foldedtoad/caliper_keyboard/images/debug_adapter_1.jpg

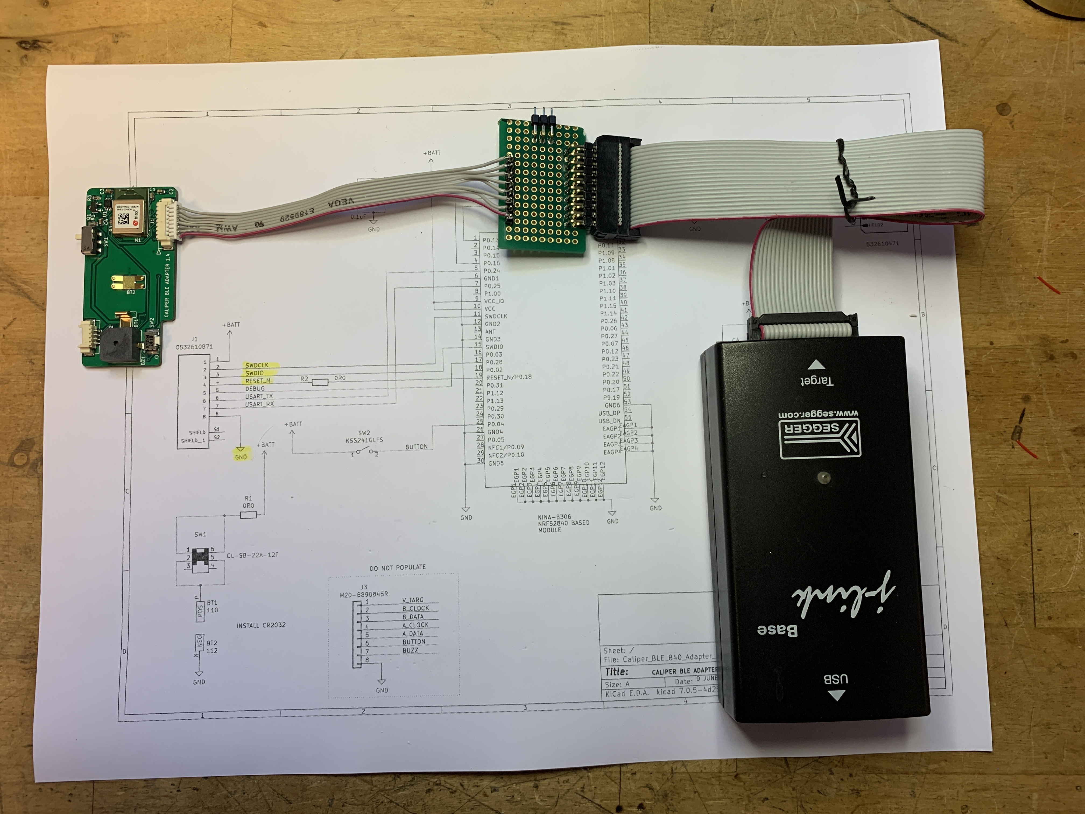
images/debug_adapter_1.jpg
