foldedtoad/caliper_keyboard/images/debug_adapter_2.jpg

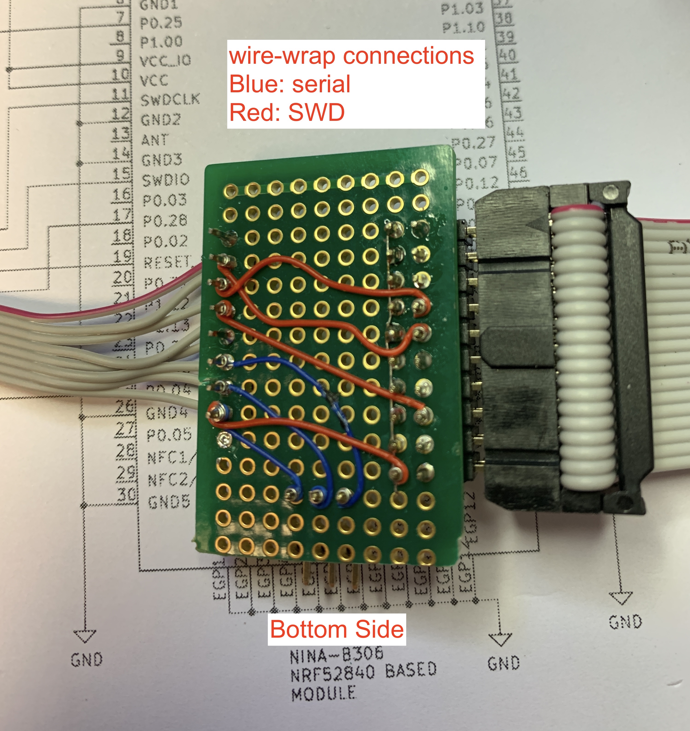
images/debug_adapter_2.jpg
