foldedtoad/caliper_keyboard/images/debug_adapter_3.JPG

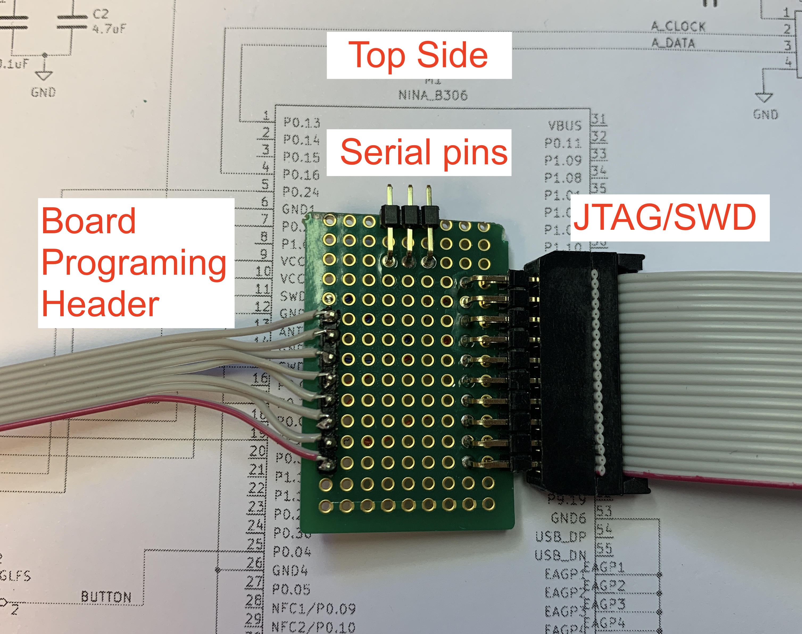
images/debug_adapter_3.JPG
