foldedtoad/caliper_keyboard/images/debug_cable.jpg

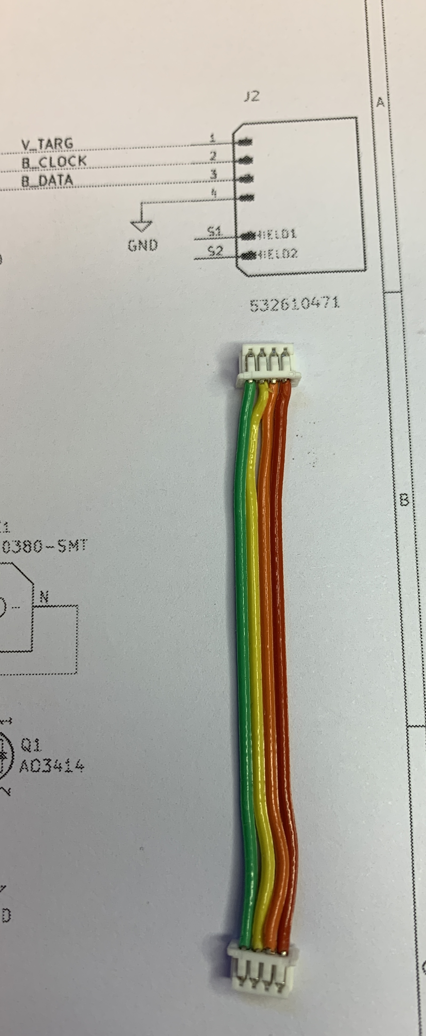
images/debug_cable.jpg
