foldedtoad/caliper_keyboard/inc/main.h

/*
 *  main.h 
 *
 *  Copyright (c) 2023   Callender-Consulting
 *
 *  SPDX-License-Identifier: Apache-2.0
 */
#ifndef __MAIN_H__
#define __MAIN_H__

/*---------------------------------------------------------------------------*/
/*                                                                           */
/*---------------------------------------------------------------------------*/

bool is_alt_running(void);

#endif /* __MAIN_H__ */
