foldedtoad/caliper_keyboard/inc/buzzer.h

/*
 *  buzzer.h  -- buzzer driver
 *
 *  Copyright (c) 2023   Callender-Consulting
 *
 *  SPDX-License-Identifier: Apache-2.0
 */
#ifndef __BUZZER_H__
#define __BUZZER_H__

#include <zephyr/kernel.h>

typedef enum {
    BUZZER_PLAY_DONE = 0,
    BUZZER_PLAY_TONE,
    BUZZER_PLAY_QUIET,
} buzzer_play_action_t;

typedef struct {
    buzzer_play_action_t  action;    // see enum above
    int                   duration;  // in milliseconds
} buzzer_play_t;

/* Duratiion is in milliseconds */

void     buzzer_init(void);
uint32_t buzzer_play(buzzer_play_t * playlist);

#endif /* __BUZZER_H__ */
