foldedtoad/caliper_keyboard/inc/ble_alt.h

/*
 *  ble_alt.h
 */
#ifndef __BLE_ALT_H__
#define __BLE_ALT_H__

#include <stdbool.h>

/*---------------------------------------------------------------------------*/
/*                                                                           */
/*---------------------------------------------------------------------------*/
#define ALTERNATE_BT_DEVICE_NAME "Caliper Shell"
#define ALTERNATE_BT_NUS_AUTHEN 0

/*---------------------------------------------------------------------------*/
/*                                                                           */
/*---------------------------------------------------------------------------*/
int ble_alt_init(void);

#endif  // __BLE_ALT_H__
