foldedtoad/caliper_keyboard/inc/tones.h

/*
 *  tpmes.h  -- predefined tones
 *
 *  Copyright (c) 2023   Callender-Consulting
 *
 *  SPDX-License-Identifier: Apache-2.0
 */
#ifndef __TONES_H__
#define __TONES_H__

#include "buzzer.h"

/*---------------------------------------------------------------------------*/
/* Collection of sounds and tones                                            */
/*---------------------------------------------------------------------------*/

extern buzzer_play_t startup_sound;
extern buzzer_play_t send_completed_sound;
extern buzzer_play_t caliper_off_sound;
extern buzzer_play_t ble_not_connected_sound;
extern buzzer_play_t error_sound;

#endif /* __TONES_H__ */
