foldedtoad/caliper_keyboard/inc/shell.h

/*
 *   shell.h
 */
#ifndef __SHELL_H
#define __SHELL_H

/*---------------------------------------------------------------------------*/
/*                                                                           */
/*---------------------------------------------------------------------------*/
int caliper_shell_init(void);

#endif  /* __SHELL_H */
