foldedtoad/caliper_keyboard/inc/watchdog.h

/*
 *   watchdog.h
 */
#ifndef __WATCHDOG_H
#define __WATCHDOG_H

/*---------------------------------------------------------------------------*/
/*                                                                           */
/*---------------------------------------------------------------------------*/
void watchdog_init(void);


#endif  /* __WATCHDOG_H */
